kelvinhall05/Southpaw75/Case/southpawcase.png

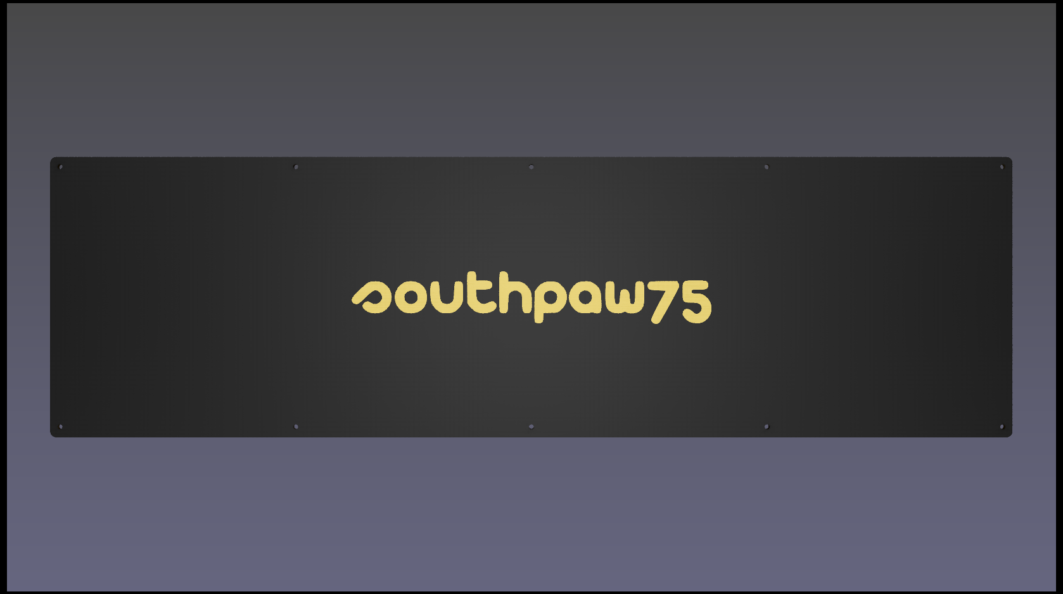
Case/southpawcase.png
