kelvinhall05/Southpaw75/Pictures/IMG_20200803_122925.jpg

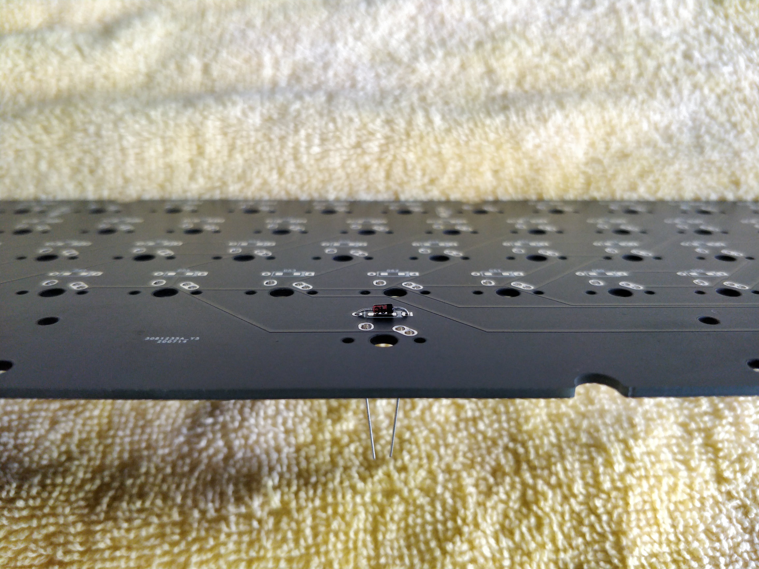
Pictures/IMG_20200803_122925.jpg
