kelvinhall05/Southpaw75/Pictures/IMG_20200803_123227.jpg

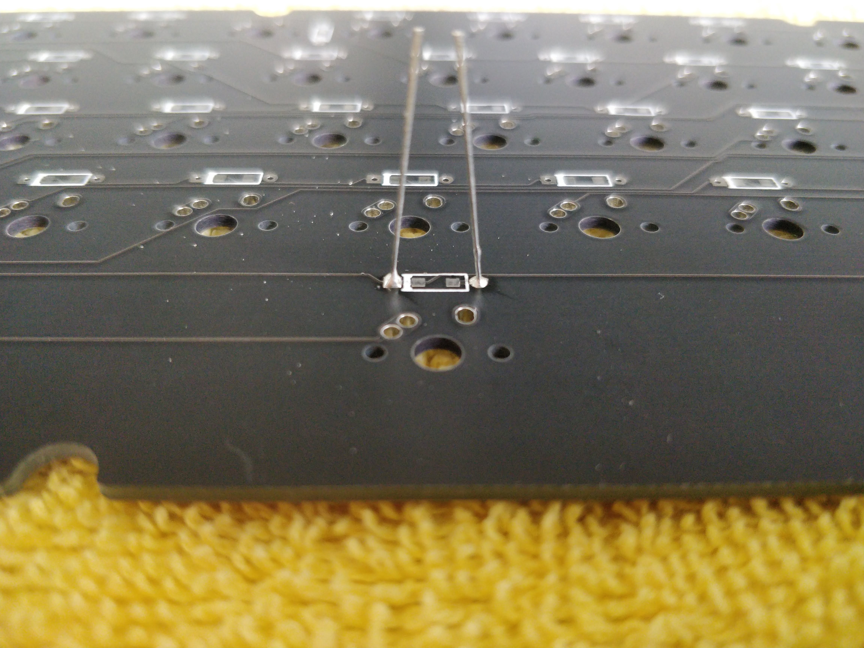
Pictures/IMG_20200803_123227.jpg
