kelvinhall05/Southpaw75/Pictures/IMG_20200803_123555.jpg

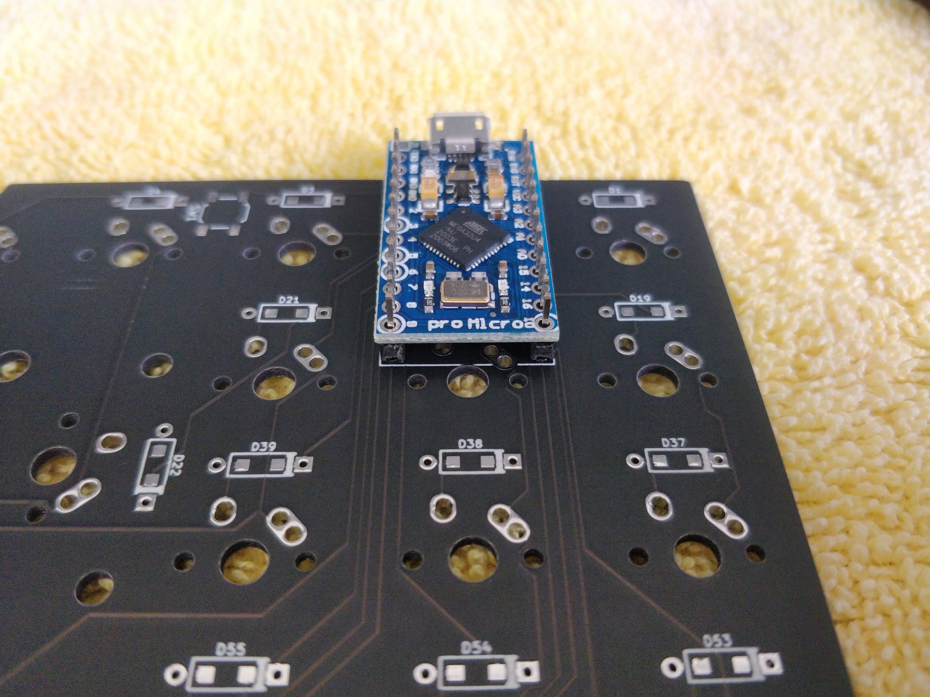
Pictures/IMG_20200803_123555.jpg
