kelvinhall05/Southpaw75/Pictures/IMG_20200803_124639.jpg

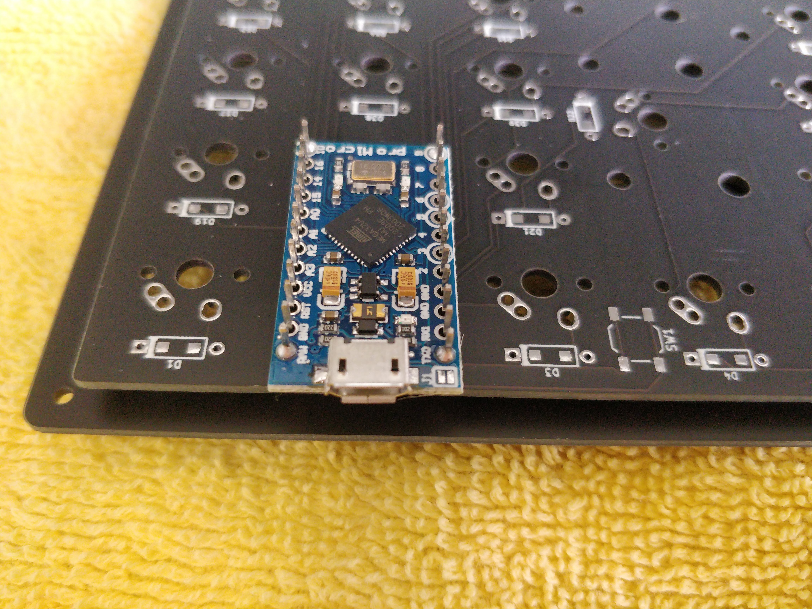
Pictures/IMG_20200803_124639.jpg
