kelvinhall05/Southpaw75/Pictures/IMG_20200803_125230.jpg

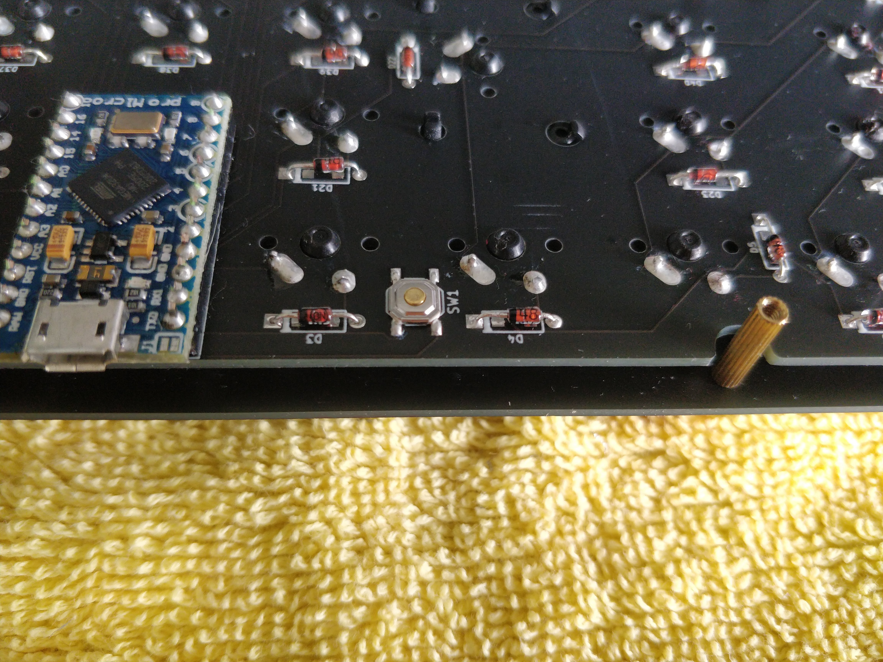
Pictures/IMG_20200803_125230.jpg
