kelvinhall05/Southpaw75/Pictures/IMG_20200803_125329.jpg

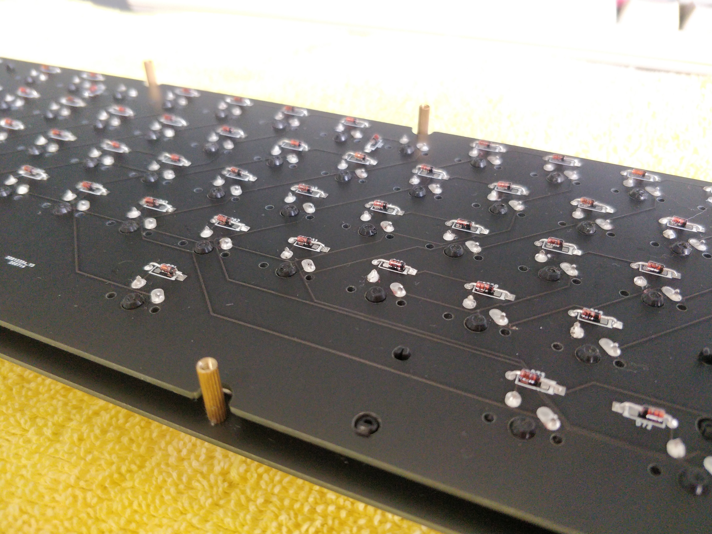
Pictures/IMG_20200803_125329.jpg
