kelvinhall05/Southpaw75/Plate/southpawplate.png

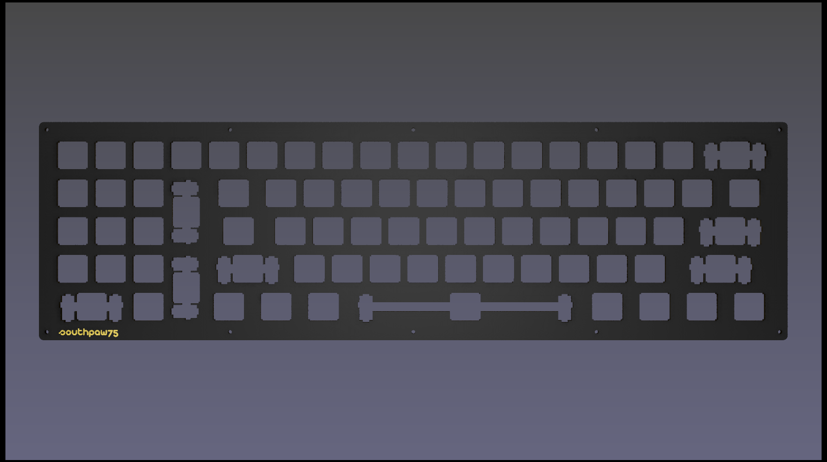
Plate/southpawplate.png
